JochiSt/MAX31865_I2C/firmware/usart.c

/*----------------------------------------------------------------------------
 Copyright:      Radig Ulrich  mailto: mail@ulrichradig.de
 Author:         Radig Ulrich
 Remarks:
 known Problems: none
 Version:        14.06.2007
 Description:    RS232 Routinen

 Dieses Programm ist freie Software. Sie können es unter den Bedingungen der
 GNU General Public License, wie von der Free Software Foundation veröffentlicht,
 weitergeben und/oder modifizieren, entweder gemäß Version 2 der Lizenz oder
 (nach Ihrer Option) jeder späteren Version.

 Die Veröffentlichung dieses Programms erfolgt in der Hoffnung,
 daß es Ihnen von Nutzen sein wird, aber OHNE IRGENDEINE GARANTIE,
 sogar ohne die implizite Garantie der MARKTREIFE oder der VERWENDBARKEIT
 FÜR EINEN BESTIMMTEN ZWECK. Details finden Sie in der GNU General Public License.

 Sie sollten eine Kopie der GNU General Public License zusammen mit diesem
 Programm erhalten haben.
 Falls nicht, schreiben Sie an die Free Software Foundation,
 Inc., 59 Temple Place, Suite 330, Boston, MA 02111-1307, USA.
------------------------------------------------------------------------------*/

#include "usart.h"
#include <stdlib.h>
#include <stdarg.h>
#include <ctype.h>
#include <string.h>
#include <avr/io.h>

volatile unsigned char buffercounter = 0;
char usart_rx_buffer[BUFFER_SIZE];

//----------------------------------------------------------------------------
//Initialisation of Serial Port
void usart_init(unsigned long baudrate)
{
	// Set the Divider
	UBRR0L = (F_CPU / (baudrate * 16L) - 1) & 0x00FF;
	UBRR0H = (((F_CPU / (baudrate * 16L) - 1) & 0xFF00)>>8);
	// Enable TXEN in the UCR TX-Data enable register
	UCR = (1 << TXEN |1 << RXEN | 1<< RXCIE);
}

//----------------------------------------------------------------------------

/**
 * print a single character on the serial port.
 * function ensures \r\n line endings
 * @param c character to be printed
 */
void usart_write_char(char c)
{
	if (c == '\n')
		usart_write_char('\r');
	// wait until previous character is sent
	while(!(USR & (1<<UDRE)));
	// output of character
	UDR = c;
	return;
}

//------------------------------------------------------------------------------
void usart_write_P (const char *Buffer,...)
{
	va_list ap;
	va_start (ap, Buffer);

	int format_flag;
	char str_buffer[10];
	char str_null_buffer[10];
	char move = 0;
	char Base = 0;
	int tmp = 0;
	char by;
	char *ptr;

	// output of all characters
    for(;;)
	{
		by = pgm_read_byte(Buffer++);
		if(by==0) break; // end of format string

		if (by == '%')
		{
            by = pgm_read_byte(Buffer++);
			if (isdigit(by)>0)
				{

 				str_null_buffer[0] = by;
				str_null_buffer[1] = '\0';
				move = atoi(str_null_buffer);
                by = pgm_read_byte(Buffer++);
				}

			switch (by)
				{
                case 's':
                    ptr = va_arg(ap,char *);
                    while(*ptr) { usart_write_char(*ptr++); }
                    break;
				case 'b':
					Base = 2;
					goto ConversionLoop;
				case 'c':
					//Int to char
					format_flag = va_arg(ap,int);
					usart_write_char (format_flag++);
					break;
				case 'i':
					Base = 10;
					goto ConversionLoop;
				case 'o':
					Base = 8;
					goto ConversionLoop;
				case 'x':
					Base = 16;
					//****************************
					ConversionLoop:
					//****************************
					itoa(va_arg(ap,int),str_buffer,Base);
					int b=0;
					while (str_buffer[b++] != 0){};
					b--;
					if (b<move)
						{
						move -=b;
						for (tmp = 0;tmp<move;tmp++)
							{
							str_null_buffer[tmp] = '0';
							}
						//tmp ++;
						str_null_buffer[tmp] = '\0';
						strcat(str_null_buffer,str_buffer);
						strcpy(str_buffer,str_null_buffer);
						}
					usart_write_str (str_buffer);
					move =0;
					break;
				}

			}
		else
		{
			usart_write_char ( by );
		}
	}
	va_end(ap);
}

//----------------------------------------------------------------------------
/**
 * output of a string
 * @param str string, which should be sent
 */
void usart_write_str(char *str)
{
	while (*str)
	{
		usart_write_char(*str++);
	}
}

//----------------------------------------------------------------------------
/**
 * Interrupt routine for receiving a single character
 */
ISR (USART_RX)
{
    unsigned char receive_char;
    receive_char = (UDR);

    #if USART_ECHO
    usart_write_char(receive_char);
    #endif

    if (usart_status.usart_ready)
    {
        usart_status.usart_rx_ovl = 1;
        return 0;
    }

    if (receive_char == 0x08)
    {
        if (buffercounter) buffercounter--;
        return 0;
    }

    if (receive_char == '\r' && (!(usart_rx_buffer[buffercounter-1] == '\\')))
    {
        usart_rx_buffer[buffercounter] = 0;
        buffercounter = 0;
        usart_status.usart_ready = 1;
        return 0;
    }

    if (buffercounter < BUFFER_SIZE - 1)
    {
        usart_rx_buffer[buffercounter++] = receive_char;
    }
    return 0;
}
